omarKmekkawy/Interfacing-Laptop-Battery-With-RaspberryPi/Images/P_20230126_201519.jpg

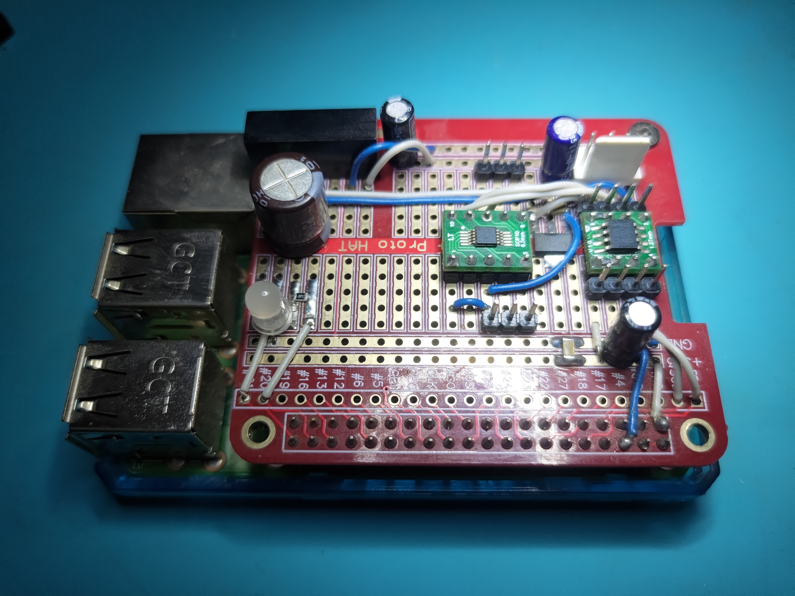
Images/P_20230126_201519.jpg
