omarKmekkawy/Interfacing-Laptop-Battery-With-RaspberryPi/Images/WIN_20230126_20_08_16_Pro.jpg

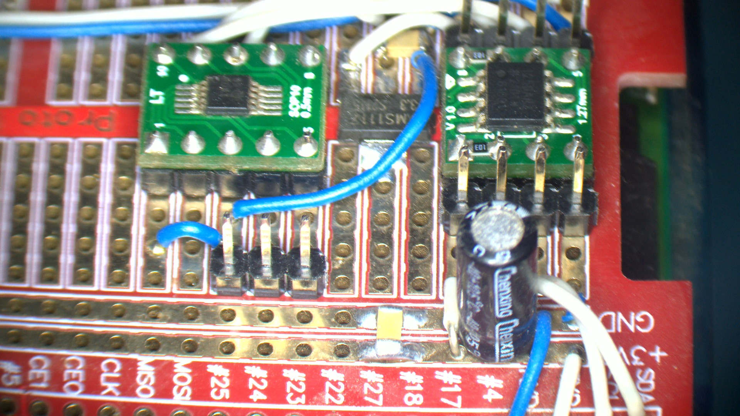
Images/WIN_20230126_20_08_16_Pro.jpg
