omarKmekkawy/Interfacing-Laptop-Battery-With-RaspberryPi/Hardware/RaspberryPi_I2C_Isolator/RaspberryPi_I2C_Isolator.kicad_pcb

## KiCad design electrical/source/weather-station.kicad_sch

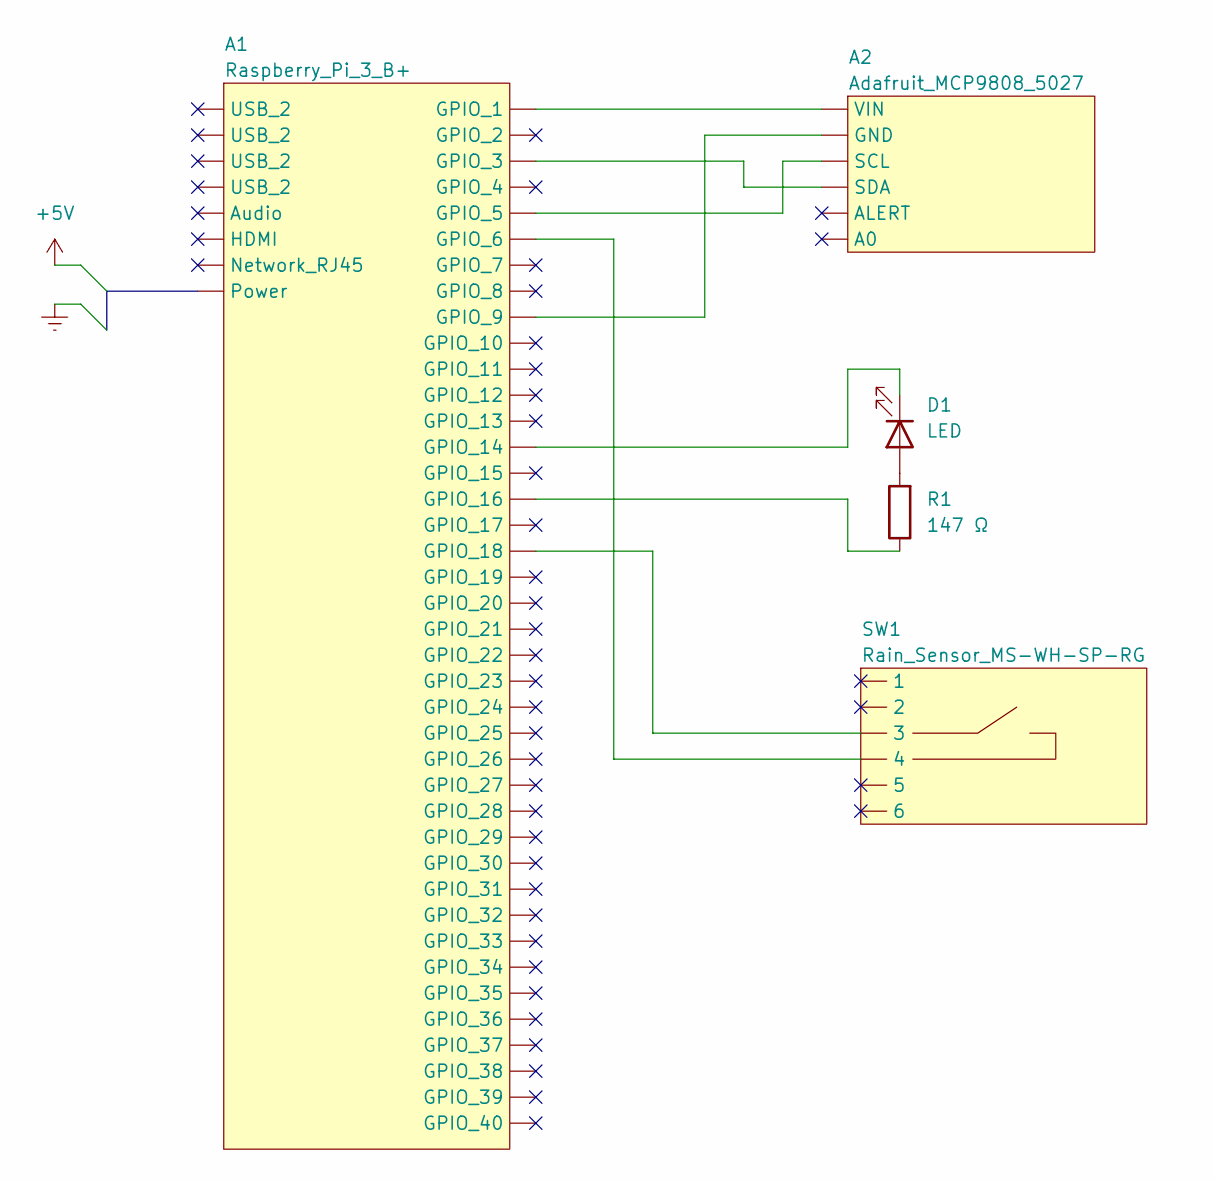
[picture p16: schematic weather-station.kicad_sch]

Parts:
A1: Raspberry_Pi_3_B+
A2: Adafruit_MCP9808_5027
D1: LED
R1: 147 Ω
SW1: Rain_Sensor_MS-WH-SP-RG

Connections:
unnamed: A1., A2., D1.1 (K), R1.1, SW1.
unnamed: D1.2 (A), R1.2
